Quorth/mesh_airsoft_targets/target_master/lib_target.h

typedef struct {
  uint8_t led_id;
  uint8_t pattern;
  uint8_t R;
  uint8_t G;
  uint8_t B;
} led_command;

unsigned long display_timer=0;
//Target node prototypes and declarations
#ifdef TARGET_NODE

#define NODE_ID 2
#define NUM_LEDS 1
boolean int_flag = 0;
boolean int_proc = 0;
uint8_t frame = 0;
const int led_pinout[NUM_LEDS][3] = {{3,5,6}};
led_command lc[NUM_LEDS];

#define NUM_ANIMATIONS 4
const uint8_t mask_frame[NUM_ANIMATIONS][24] = {
                                   {8,8,8,8,8,8,8,8,8,8,8,8,8,8,8,8,8,8,8,8,8,8,8,8},
                                   {0,0,0,0,0,0,0,0,0,0,0,0,0,0,0,0,0,0,0,0,0,0,0,0},
                                   {0,0,0,0,0,0,0,0,0,0,0,0,8,8,8,8,8,8,8,8,8,8,8,8},
                                   {0,0,0,0,0,0,8,8,8,8,8,8,0,0,0,0,0,0,8,8,8,8,8,8}
                                  };

#endif

#ifdef TARGET_MASTER

led_command lc;
uint8_t game = 0;
uint8_t game_state = 0;
uint32_t time = 0;
// Game 1 Variables
uint8_t current = 0;
const led_command lc_on = {0,1,0,255,0};

#endif
